JFinnbarrM/BlowChain/reference_code/niall/p2/t4/mylib_sampling/include/mylib_sampling_json.h

#include <zephyr/drivers/sensor_data_types.h>
#include <zephyr/drivers/rtc.h>

void jsonify_samples(struct rtc_time* rtc_time_ptr, 
    struct sensor_q31_data *data_array, int *did_array, size_t count);
